shawnpinciara/dewi/src/blender/bocchino.stl

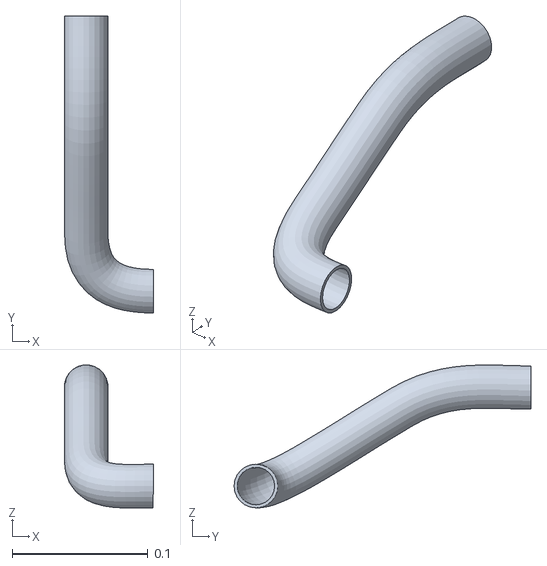
[picture p16: CAD file, 2023-07-20, last stored version]
src/blender/bocchino.stl
0.0654 x 0.219 x 0.105
