shawnpinciara/dewi/src/forma.stl

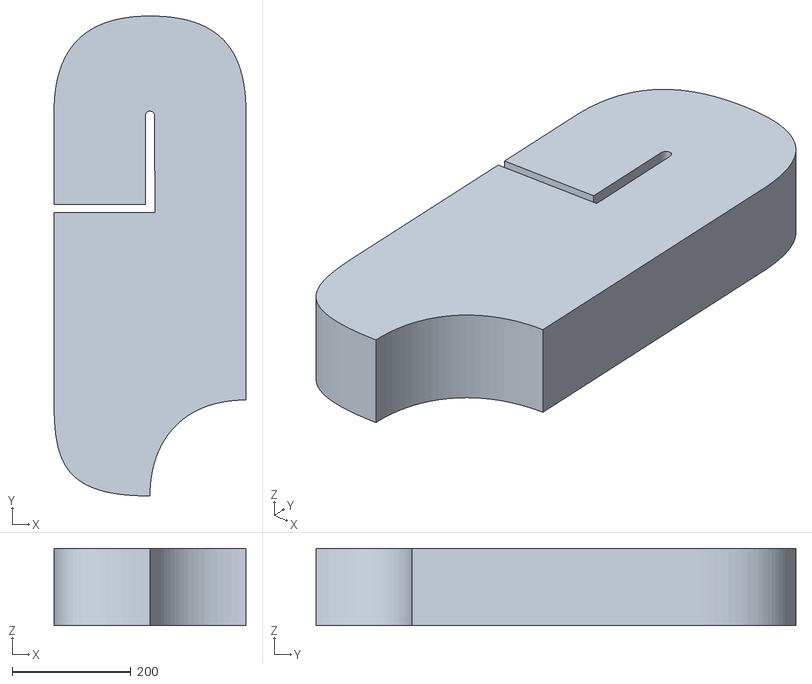
[picture p17: CAD file, 2023-09-09, last stored version]
src/forma.stl
324.0 x 810.0 x 130.0
