shawnpinciara/dewi/src/blender/bocchino 3d print.stl

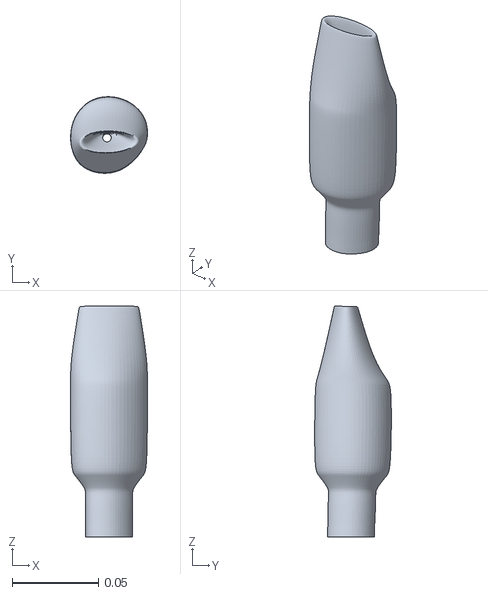
[picture p18: CAD file, 2023-07-20, last stored version]
src/blender/bocchino 3d print.stl
0.0445 x 0.0444 x 0.134
